GirishTabaraddi/24Ghz_RADAR_for_Movement_Detection/KiCad_LabProject/20_release/230417_Lab1_SDHD_GroupD3_1.0/10_Report/Technische-Spezifikation-PCB-Anfrage_Bestellung.xls

Sheet: technischeSpezifikation
Anfrage
Leiterplattenspezifikation
 |  |  |  |  |  | Datum | 2020-01-23
Projektname: |  |  | LP-Bezeichn.: |  |  | Rev.:
Allgemeine Anforderungen |  |  |  | Produktions-Anforderungen
IPC-A-600 G |  | Class II |  | LP-Typ: |  |  |  | Starr
RoHS kompatibel |  | Ja |  | LP-Größe: |  | +/- 0,2 mm
UL-Zertifizierung |  | Ja |  | Nutzen: |  |  |  | Nein
Hersteller Logo |  | Ja |  | Nutzengröße: |  | +/- 0,2 mm
Date Code |  | Ja |  | Stück pro Nutzen:
E-Test |  | Ja |  | Kontur: |  |  |  | gefräst
Impedanzkontrolle |  | Ja |  | LP-Endstärke über alles: |  | +/- 10%
Erstmusterprüfbericht |  | Nein |  | Lagenanzahl:
Schliffbild |  | Nein |  | Innenlagenkupfer incl. galv. Cu: |  | (µm)
Position der UL-Nr.und Logo |  | in Daten |  | Außenlagenkupfer incl. galv. Cu: |  | (µm)
Position Hersteller Logo |  | spezifiziert, |  | kleinste Leiterbahnbreite |  | (µm)
und Datecode |  | Design in Cu |  | kleinster Leiterbahnabstand |  | (µm)
 |  |  |  | Lötoberfläche: |  |  |  | chem. NI/AU
 |  |  |  | Steckergold: |  |  |  | Nein
Bohrparameter |  |  |  | Lötstoplack: |  |  |  | Grün
kleinster Bohrendurchmesser (µm) |  |  |  | Bestückungsdruck: |  |  |  | ohne
Anzahl Bohrungen pro LP (Stück) |  |  |  | Farbe d. Bestückungsdruck: |  |  |  | ohne
Langlöcher |  | Nein |  | einseitiger Viadruck: |  |  |  | Nein
Randkontaktierung |  | Nein |  | Carbondruck: |  |  |  | Nein
Backdrill |  | Nein |  | Abziehlack: |  |  |  | Nein
Blind Via |  | Ja
Blind Via / Bohrebenen |  | 1-2, 9-10
Buried Via |  | Nein |  | Basismaterial
Buried Via / Bohrebenen |  |  |  | Material: |  |  |  | FR4
Microfill der Blind Via |  | Ja |  | gefülltes System: |  |  |  | Ja
Pluggen der Buried Via |  | Nein |  | TG-Wert: |  | ° Celsius |  | 150
 |  |  |  | Hersteller: |  |  |  | Matsusihita
 |  |  |  | Materialbezeichnung: |  |  |  | R 1566W / TG 150°C
 | Einkauf
Rechnungsanschrift: |  |  |  | Einzelstückzahl:
 |  |  |  | Nutzenstückzahl:
 |  |  |  | Lieferzeit:
 |  |  |  | Versandart:
Lieferanschrift: |  |  |  | Eintrefftermin:
Kontakt Einkauf: |  |  |  |  | Kontakt Technik:
Ansprechpartner: |  |  |  | Ansprechpartner:
Email: |  |  |  | Email:
Telefon: |  |  |  | Telefon:
Fax: |  |  |  | Fax:
Besonderheiten:
technisches Datenblatt V2 (26.11.2008) created by Bertram / Süßlin © Elekonta Marek GmbH & Co. KG www.elekonta.de

Sheet: Lagenaufbau
Datum: | 2020-01-23 | Ansprechpartner: | 0
Projektname: | 0 | Email: | 0
LP-Bezeichnung: | 0 | Telefon: | 0
Revisionsstand: | 0 | Fax: | 0
technisches Datenblatt V2 (26.11.2008) created by Bertram / Süßlin © Elekonta Marek GmbH & Co. KG www.elekonta.de

Sheet: Nutzenzeichnung
Datum: | 2020-01-23 |  | Ansprechpartner: | 0
Projektname: | 0 |  | Email: | 0
LP-Bezeichnung: | 0 |  | Telefon: | 0
Revisionsstand: | 0 |  | Fax: | 0
 |  | Nutzenzeichnung
technisches Datenblatt V2 (26.11.2008) created by Bertram / Süßlin © Elekonta Marek GmbH & Co. KG www.elekonta.de
